arnova/pvboiler/platformio/include/PvBoiler.h

#pragma once
#ifndef PVBOILER_H
#define PVBOILER_H

#include <elapsedMillis.h>
#include <OneWire.h>
#include <DallasTemperature.h>

#include "system.h"
#include "Uptime.h"
#include "Network.h"
#include "PvBoilerCommandHandler.h"
#include "RollingAverage.h"
#include "Legionella.h"

// Triac phase control firing delay lookup table
// Index = power percentage (0-100)
// Value = firing delay as fraction of half-period (0.0 = start, 1.0 = end)
// Formula: P/Pmax = 1 - alpha/pi + sin(2*alpha)/(2*pi)
const float triac_percentage_factor[101] =
{
  // 0-9%
  1.0000f, 0.8840f, 0.8531f, 0.8310f, 0.8132f, 0.7980f, 0.7846f, 0.7724f, 0.7612f, 0.7508f,
  // 10-19%
  0.7411f, 0.7319f, 0.7231f, 0.7147f, 0.7067f, 0.6990f, 0.6915f, 0.6842f, 0.6772f, 0.6704f,
  // 20-29%
  0.6637f, 0.6572f, 0.6508f, 0.6445f, 0.6384f, 0.6324f, 0.6264f, 0.6206f, 0.6149f, 0.6092f,
  // 30-39%
  0.6036f, 0.5980f, 0.5926f, 0.5871f, 0.5818f, 0.5765f, 0.5712f, 0.5659f, 0.5607f, 0.5556f,
  // 40-49%
  0.5504f, 0.5453f, 0.5402f, 0.5351f, 0.5301f, 0.5251f, 0.5200f, 0.5150f, 0.5100f, 0.5050f,
  // 50-59%
  0.5000f, 0.4950f, 0.4900f, 0.4850f, 0.4800f, 0.4749f, 0.4699f, 0.4649f, 0.4598f, 0.4547f,
  // 60-69%
  0.4496f, 0.4444f, 0.4393f, 0.4341f, 0.4288f, 0.4235f, 0.4182f, 0.4129f, 0.4074f, 0.4020f,
  // 70-79%
  0.3964f, 0.3908f, 0.3851f, 0.3794f, 0.3736f, 0.3676f, 0.3616f, 0.3555f, 0.3492f, 0.3428f,
  // 80-89%
  0.3363f, 0.3296f, 0.3228f, 0.3158f, 0.3085f, 0.3010f, 0.2933f, 0.2853f, 0.2769f, 0.2681f,
  // 90-99%
  0.2589f, 0.2492f, 0.2388f, 0.2276f, 0.2154f, 0.2020f, 0.1868f, 0.1690f, 0.1469f, 0.1160f,
  // 100-100%
  0.0000f
};

class CPvBoiler
{
  public:
    CPvBoiler(CNetwork& network);

    enum dim_style_e
    {
      DIM_STYLE_NONE = 0,
      DIM_STYLE_PHASE_ANGLE,
      DIM_STYLE_SSR
    };
    typedef enum dim_style_e dim_style_t;

    enum mode_e
    {
      MODE_BUDGET = 0,
      MODE_PERCENT,
      MODE_OFF,
      MODE_BOOST
    };
    typedef enum mode_e mode_t;

    void Loop();
    void Reset();

    bool MqttPublishValues(const bool bForce = false);
    void MqttPublishConfig();
    void LoadSettings();
    void FactoryReset();

    void TrigNetworkWatchdog() { m_iNetworkWatchdogCounter = 0; };

    void SetPowerBudget(const int32_t iVal) { m_iPowerBudget = iVal; m_bPublishPowerBudget = true; };
    void SetPowerPercentage(const uint8_t iVal) { m_iPowerPercentage = iVal; m_bPublishPowerPercentage = true; };

    void SetBoilerPowerRating(const uint16_t iPower);
    void SetDeadZone(const uint8_t iDeadZone);
    void SetBudgetMargin(const uint16_t iMargin);
    void SetMode(const mode_t mode);
    void SetDimStyle(const dim_style_t dimStyle);
    void SetSsrPeriodCount(const uint8_t iPeriod);
    void SetErrorGainPos(const float fGain);
    void SetErrorGainNeg(const float fGain);
    void SetStepClampPos(const float fClamp);
    void SetStepClampNeg(const float fClamp);
    void SetMqttUpdateInterval(const uint8_t iInterval);
    void SetNetWatchDogTimeout(const uint16_t iTimeout);
    void SetNetWatchDogRecovery(const uint16_t iTimeout);

    float GetCurrentPercentage() const { return m_fCurrentPercentage; };
    uint16_t GetCurrentPower() const { return (m_fCurrentPercentage * m_iBoilerPowerRating) / 100; };

    uint16_t CalculateTriacPhaseDelay(const uint16_t iPeriodTime, const uint16_t iZeroCrossWindow);
    float GetTriacAngleFactor() const { return m_fTriacAngleFactor; };
    uint16_t GetTriacPhaseAngle() const { return m_iTriacPhaseAngle; };

    int32_t GetPowerBudget() const { return m_iPowerBudget; };
    uint8_t GetPowerPercentage() const { return m_iPowerPercentage; };

    uint16_t GetBoilerPowerRating() const { return m_iBoilerPowerRating; };
    uint8_t GetDeadZone() const { return m_iDeadZone; };
    uint16_t GetBudgetMargin() const { return m_iBudgetMargin; };
    mode_t GetMode() const { return m_mode; };
    dim_style_t GetDimStyle() const { return m_dimStyle; };
    uint8_t GetSsrPeriodCount() const { return m_iSsrPeriodCount; };
    float GetErrorGainPos() const { return m_fErrorGainPos; };
    float GetErrorGainNeg() const { return m_fErrorGainNeg; };
    float GetStepClampPos() const { return m_fStepClampPos; };
    float GetStepClampNeg() const { return m_fStepClampNeg; };
    uint16_t GetMainsPeriod() const { return m_iPeriodTime; };
    uint16_t GetMainsZeroCrossWindow() const { return m_iZeroCrossWindow; };
    uint16_t GetNetWatchDogTimeout() const { return m_iNetWatchDogTimeout; };
    uint16_t GetNetWatchDogRecovery() const { return m_iNetWatchDogRecovery; };
    uint8_t GetMqttUpdateInterval() const { return m_iMqttUpdateInterval; };
    CUptime::uptime_t GetUpTime() const { return m_upTime.GetBreakdown(); };
    float GetBoilerTemperature() const { return m_fBoilerTemperature; };

    void SetPowerGood(const bool bPowerGood) { m_bPowerGood = bPowerGood; m_bPowerGoodFlag &= bPowerGood; };
    bool GetPowerGood() const { return m_bPowerGood; };
    bool GetPowerGoodFlag() { const bool bPowerGoodFlag = m_bPowerGoodFlag; m_bPowerGoodFlag = m_bPowerGood; return bPowerGoodFlag; };

  private:
    void Update();
    void CheckNetworkWatchDog();

    CNetwork& m_network;

    elapsedMillis m_loopTimer = 0;
    elapsedMillis m_mqttPublishTimer = 0;
    uint32_t m_iNetworkWatchdogCounter = 0;
    uint32_t m_iNetworkWatchdogRecoveryCounter = 0;

    int32_t m_iPowerBudget = 0;
    bool m_bPublishPowerBudget = true;

    uint8_t m_iPowerPercentage = 0;
    bool m_bPublishPowerPercentage = true;

    float m_fCurrentPercentage = 0.0f;
    bool m_bPublishOutputPercentage = true;

    bool m_bPublishSettings = true;

    uint16_t m_iBoilerPowerRating = BOILER_POWER_RATING_DEFAULT;  // Watt
    uint8_t m_iDeadZone = DEAD_ZONE_DEFAULT;  // Watt
    uint16_t m_iBudgetMargin = BUDGET_MARGIN_DEFAULT; // Watt

    uint8_t m_iMqttUpdateInterval = 0;
    uint16_t m_iNetWatchDogTimeout = 0;
    uint16_t m_iNetWatchDogRecovery = 0;

    // Keep track of up-time
    CUptime m_upTime;

    // Enable this to use SSR style mode instead of triac phase cut mode. This will blank/pass-through full periods like an SSR does
    CPvBoiler::dim_style_t m_dimStyle = CPvBoiler::DIM_STYLE_NONE;

    // Amount of (half) sinus / periods when ssr style mode is used. Always use an even number!
    uint8_t m_iSsrPeriodCount = 50; // (= 0.5s @ 50 Hz).

    float m_fTriacAngleFactor = 0.0f;
    uint16_t m_iTriacPhaseAngle = 0; // us
    uint16_t m_iPeriodTime = NET_PERIOD_INVALID; // us
    uint16_t m_iZeroCrossWindow = ZERO_CROSS_WINDOW_INVALID; // us
    bool m_bPowerGood = true;
    bool m_bPowerGoodFlag = true;

    // (Proportional) error gains
    float m_fErrorGainPos = ERROR_GAIN_POS_DEFAULT;
    float m_fErrorGainNeg = ERROR_GAIN_NEG_DEFAULT;

    float m_fStepClampPos = STEP_CLAMP_POS_DEFAULT;
    float m_fStepClampNeg = STEP_CLAMP_NEG_DEFAULT;

    mode_t m_mode = MODE_BUDGET; // Select if you want to control using setting power percentage or providing power budget

    OneWire m_oneWire;
    DallasTemperature m_tempSensors;
    
    float m_fBoilerTemperature = -1.0f;
    bool m_bPublishBoilerTemperature = true;
    uint16_t m_iBoilerTemperatureRetryCount = 0;
    CRollingAverage m_boilerTemperatureAverage;
    CLegionella m_legionella;
};
#endif // PVBOILER_H
