arnova/pvboiler/platformio/include/MqttClient.h

#pragma once
#ifndef MQTT_CLIENT_H
#define MQTT_CLIENT_H

#include <PubSubClient.h>
#include <ArduinoJson.h>

#include "system.h"

class CMqttClient : public PubSubClient
{
  public:
    static void PrintDataError(void);
    static void GetFriendlyName(const char* strName, char* strFriendly, const size_t iMaxSize);

    void PublishSwitchConfig(const char* strItem);
    void PublishNumberConfig(const char* strItem, const float fStep = 1.0f, const float fMin = 0.0f, const float fMax = 100.0f, const char* strUnit = "", const char* strDeviceClass = "", const bool bBox = true);
    void PublishSelectConfig(const char* strItem, const char** strValues, const uint8_t iCount);
    void PublishBinarySensorConfig(const char* strItem, const bool bDiag = false);
    void PublishSensorConfig(const char* strItem, const char* strUnit = "", const char* strDeviceClass = "", const char* strStateClass = "", const bool bDiag = false);

    void UnpublishSwitchConfig(const char* strItem);
    void UnpublishNumberConfig(const char* strItem);
    void UnpublishBinarySensorConfig(const char* strItem);
    void UnpublishSensorConfig(const char* strItem);

    bool PublishMessage(const char* strItem, const char* strPayload, const bool bRetained = true);

    void Init(const uint8_t* serverIp, const char* strHostName, const char* strUser, const char* strPassword);
    bool ServerConnect();

  private:
    void ConstructConfigMessage(JsonDocument& root, const char* strItem);
    void PublishConfig(JsonDocument& root, const char* strItem, const char* strTopicType);
    void PublishSetterConfig(JsonDocument& root, const char* strItem, const char* strTopicType);
    void PublishGetterConfig(JsonDocument& root, const char* strItem, const char* strTopicType, const bool bDiag = false);
    void UnpublishConfig(const char* strItem, const char* strTopicType, const bool bSetter = false);

    uint8_t m_serverIp[4] = { 0 };
    char m_strHostName[HOST_NAME_MAX_SIZE + 1] = { 0 };
    char m_strUser[MQTT_USER_MAX_SIZE + 1] = { 0 };
    char m_strPassword[MQTT_PASSWORD_MAX_SIZE + 1] = { 0 };
};
#endif // MQTT_CLIENT_H
