arnova/pvboiler/platformio/include/App.h

#pragma once
#ifndef APP_H
#define APP_H

#include "system.h"
#include "Network.h"
#include "PvBoiler.h"
#include "Ssd1306.h"
#include "Terminal.h"
#include "TrackedValue.h"

class CApp
{
  public:
    CApp();

    void Init();
    void UpdateValues();
    void Loop();

    void IRAM_ATTR ZeroCrossHandler();
    void IRAM_ATTR TriacGateHandler();

#ifdef ESP32
    void SetTimerHandle(hw_timer_t* hTriacTimer) { m_hTriacTimer = hTriacTimer; };
#endif

    bool CommandHandler();
    void HandleNetwork();
    void HandleDisplay();

    CNetwork& GetNetwork() { return m_network; };
    CPvBoiler& GetPvBoiler() { return m_pvBoiler; };

  private:
    void IRAM_ATTR ScheduleTriac(const uint32_t iNow);

#ifdef ESP32
    hw_timer_t *m_hTriacTimer = nullptr;
#endif

    CNetwork m_network;
    CPvBoiler m_pvBoiler;
    CPvBoilerCommandHandler m_commandHandler;
    CTerminal m_terminal;
    CSsd1306 m_display;
    uint8_t m_displayCount = 0;

    elapsedMillis m_ledTimer = 0;
    elapsedMillis m_displayTimer = 0;

    CTrackedValue m_period;
    CTrackedValue m_zeroCrossWindow;

    uint32_t m_iLastPeriodStartTime = 0; // ISR only
    uint32_t m_iLastEventTime = 0; // ISR only

    volatile bool m_bTriacOn = false;
    volatile bool m_bGateBlanking = false;
    uint8_t m_iSSRPeriodCounter = 0; // ISR only
    volatile uint16_t m_iTriacDelayUs = 0;
    volatile uint8_t m_iSSRPeriodCount = 0;
    volatile uint8_t m_iCurrentPercentage = 0;
    volatile CPvBoiler::dim_style_t m_dimStyle = CPvBoiler::DIM_STYLE_NONE;
};
#endif // APP_H
