arnova/pvboiler/platformio/include/CommandHandler.h

#pragma once
#ifndef COMMAND_HANDLER_H
#define COMMAND_HANDLER_H

#include "CommandParser.h"

// Maximum byte size for arguments stored in m_bufArg1
#define ARG_BUF_BYTE_SIZE 6

class CCommandHandler
{
  public:
    CCommandHandler() {};   // Empty ctor
    ~CCommandHandler() {};  // Empty dtor

    static result_code_t FormatIP(uint8_t *data, char *strResult);

  protected:
    result_code_t CmdEchoOnOff(const char *strArgs);
    result_code_t CmdReboot(const char *strArgs);
};

#endif // COMMAND_HANDLER_H
